tomaskovacik/audi_concert1_chorus1_volume_fix/Pics/20180920_154234.jpg

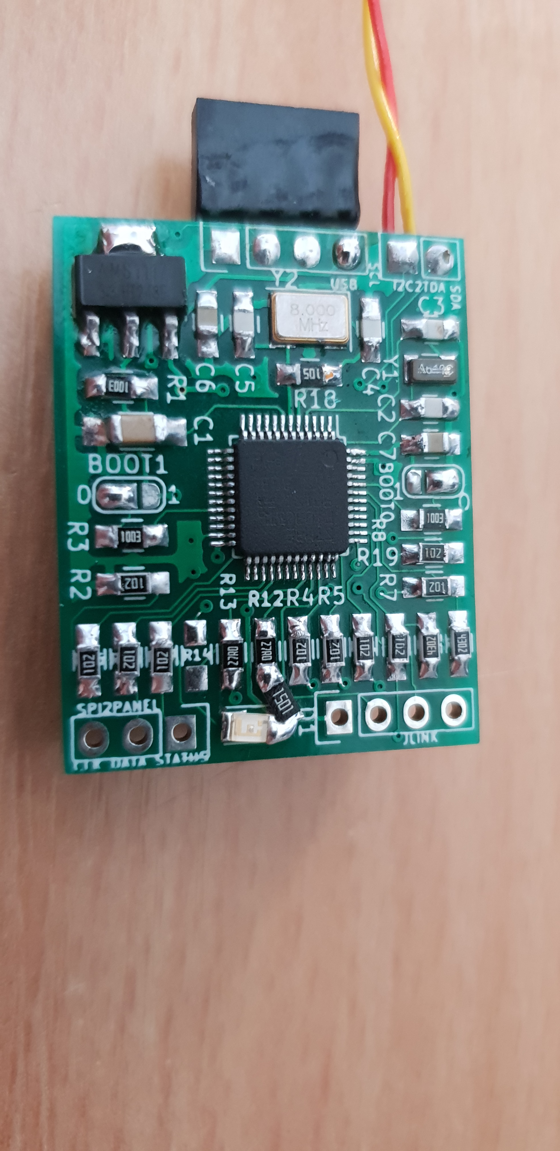
Pics/20180920_154234.jpg
