tomaskovacik/audi_concert1_chorus1_volume_fix/SW/audi_volume_fix_stm32/audi_concert_panel.h

#pragma once
#include <stdint.h>

struct Config {
  uint8_t magic[3];
  uint8_t vol;   // start volume level 1-5
  uint8_t gala;  // GALA level: 0=off, 1-5
  uint8_t ta;    // reserved
  uint8_t crc;   // vol+gala+ta checksum
};

#define PANEL_1  0x01
#define PANEL_2  0x02
#define PANEL_3  0x03
#define PANEL_4  0x04
#define PANEL_5  0x05
#define PANEL_6  0x06
#define PANEL_SEEK_UP  0x07
#define PANEL_NEXT_CD  0x07
#define PANEL_TP  0x08
#define PANEL_RDS  0x09
#define PANEL_CPS  0x0A
#define PANEL_MODE  0x0B
#define PANEL_RD  0x0C
#define PANEL_PREVIOUS_TRACK 0x0D
#define PANEL_FAST_REWIND 0x0D
#define PANEL_FADE  0x0E
#define PANEL_BALANCE  0x0F
#define PANEL_BASS  0x10
#define PANEL_AM  0x11
#define PANEL_DOLBY  0x12
#define PANEL_FAST_FORWARD 0x13
#define PANEL_NEXT_TRACK 0x13
#define PANEL_TREBLE  0x14
#define PANEL_AS  0x15
#define PANEL_SCAN  0x16
#define PANEL_FM  0x17
#define PANEL_SEEK_DOWN  0x18
#define PANEL_PREVIOUS_CD 0x18
#define PANEL_REVERSE  0x19
#define PANEL_KNOB_UP  0x86
#define PANEL_KNOB_DOWN  0x88
#define PANEL_CODE_IN  0x1E
#define PANEL_EJECT  0x1F
#define PANEL_BUTTON_RELEASE  0x21
#define PANEL_REMOTE_VOLUME_UP  0x1A
#define PANEL_REMOTE_VOLUME_DOWN  0x1B
#define PANEL_REMOTE_RIGHT 0x27
#define PANEL_REMOTE_LEFT 0x26
#define PANEL_REMOTE_UP 0x1C
#define PANEL_REMOTE_DOWN 0x1D
#define PANEL_START 0x25
